MatthewMaurier/ECE491-Portable-VIO-System/testapp/logs/vio_pose_20260222_155116.csv

unix_time | iso_time | x | y | z | roll_deg | pitch_deg | yaw_deg
1771800676.1259048 | 2026-02-22T22:51:16.125905+00:00 | -0.08419236465883269 | -0.03830850785238065 | 0.04034426217589812 | 173.38593449884826 | -69.28563379189045 | 3.382155419367111
1771800676.1280463 | 2026-02-22T22:51:16.128046+00:00 | -0.08457439908171875 | -0.03807717124405796 | 0.040868852388672605 | 173.39800622198064 | -69.3585202448284 | 3.4002216375230327
1771800676.1289172 | 2026-02-22T22:51:16.128917+00:00 | -0.08489986783532417 | -0.037859156838746875 | 0.04131441325726466 | 173.4040341967794 | -69.42143132253412 | 3.427149264233639
1771800676.1294217 | 2026-02-22T22:51:16.129422+00:00 | -0.08522439287485799 | -0.03763587569367845 | 0.04175026050617513 | 173.41200757454803 | -69.4868799863369 | 3.4512420397038075
1771800676.1297686 | 2026-02-22T22:51:16.129769+00:00 | -0.08555238587579522 | -0.03742313051109714 | 0.042166488016533686 | 173.4184105107795 | -69.54490691514856 | 3.467179249033701
1771800676.1300893 | 2026-02-22T22:51:16.130089+00:00 | -0.08588750251244005 | -0.037225582957783825 | 0.042561717527170896 | 173.4235810266253 | -69.59528757027837 | 3.4731153113466786
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
